juarendra/ERGODASH-MOD-ENCH-OLED-QMK_VIA/Hardware/PCB/Rev1.2/ergodash.kicad_sch

## KiCad design Hardware/PCB/Rev1.2/ergodash.kicad_sch (2024-04-25)

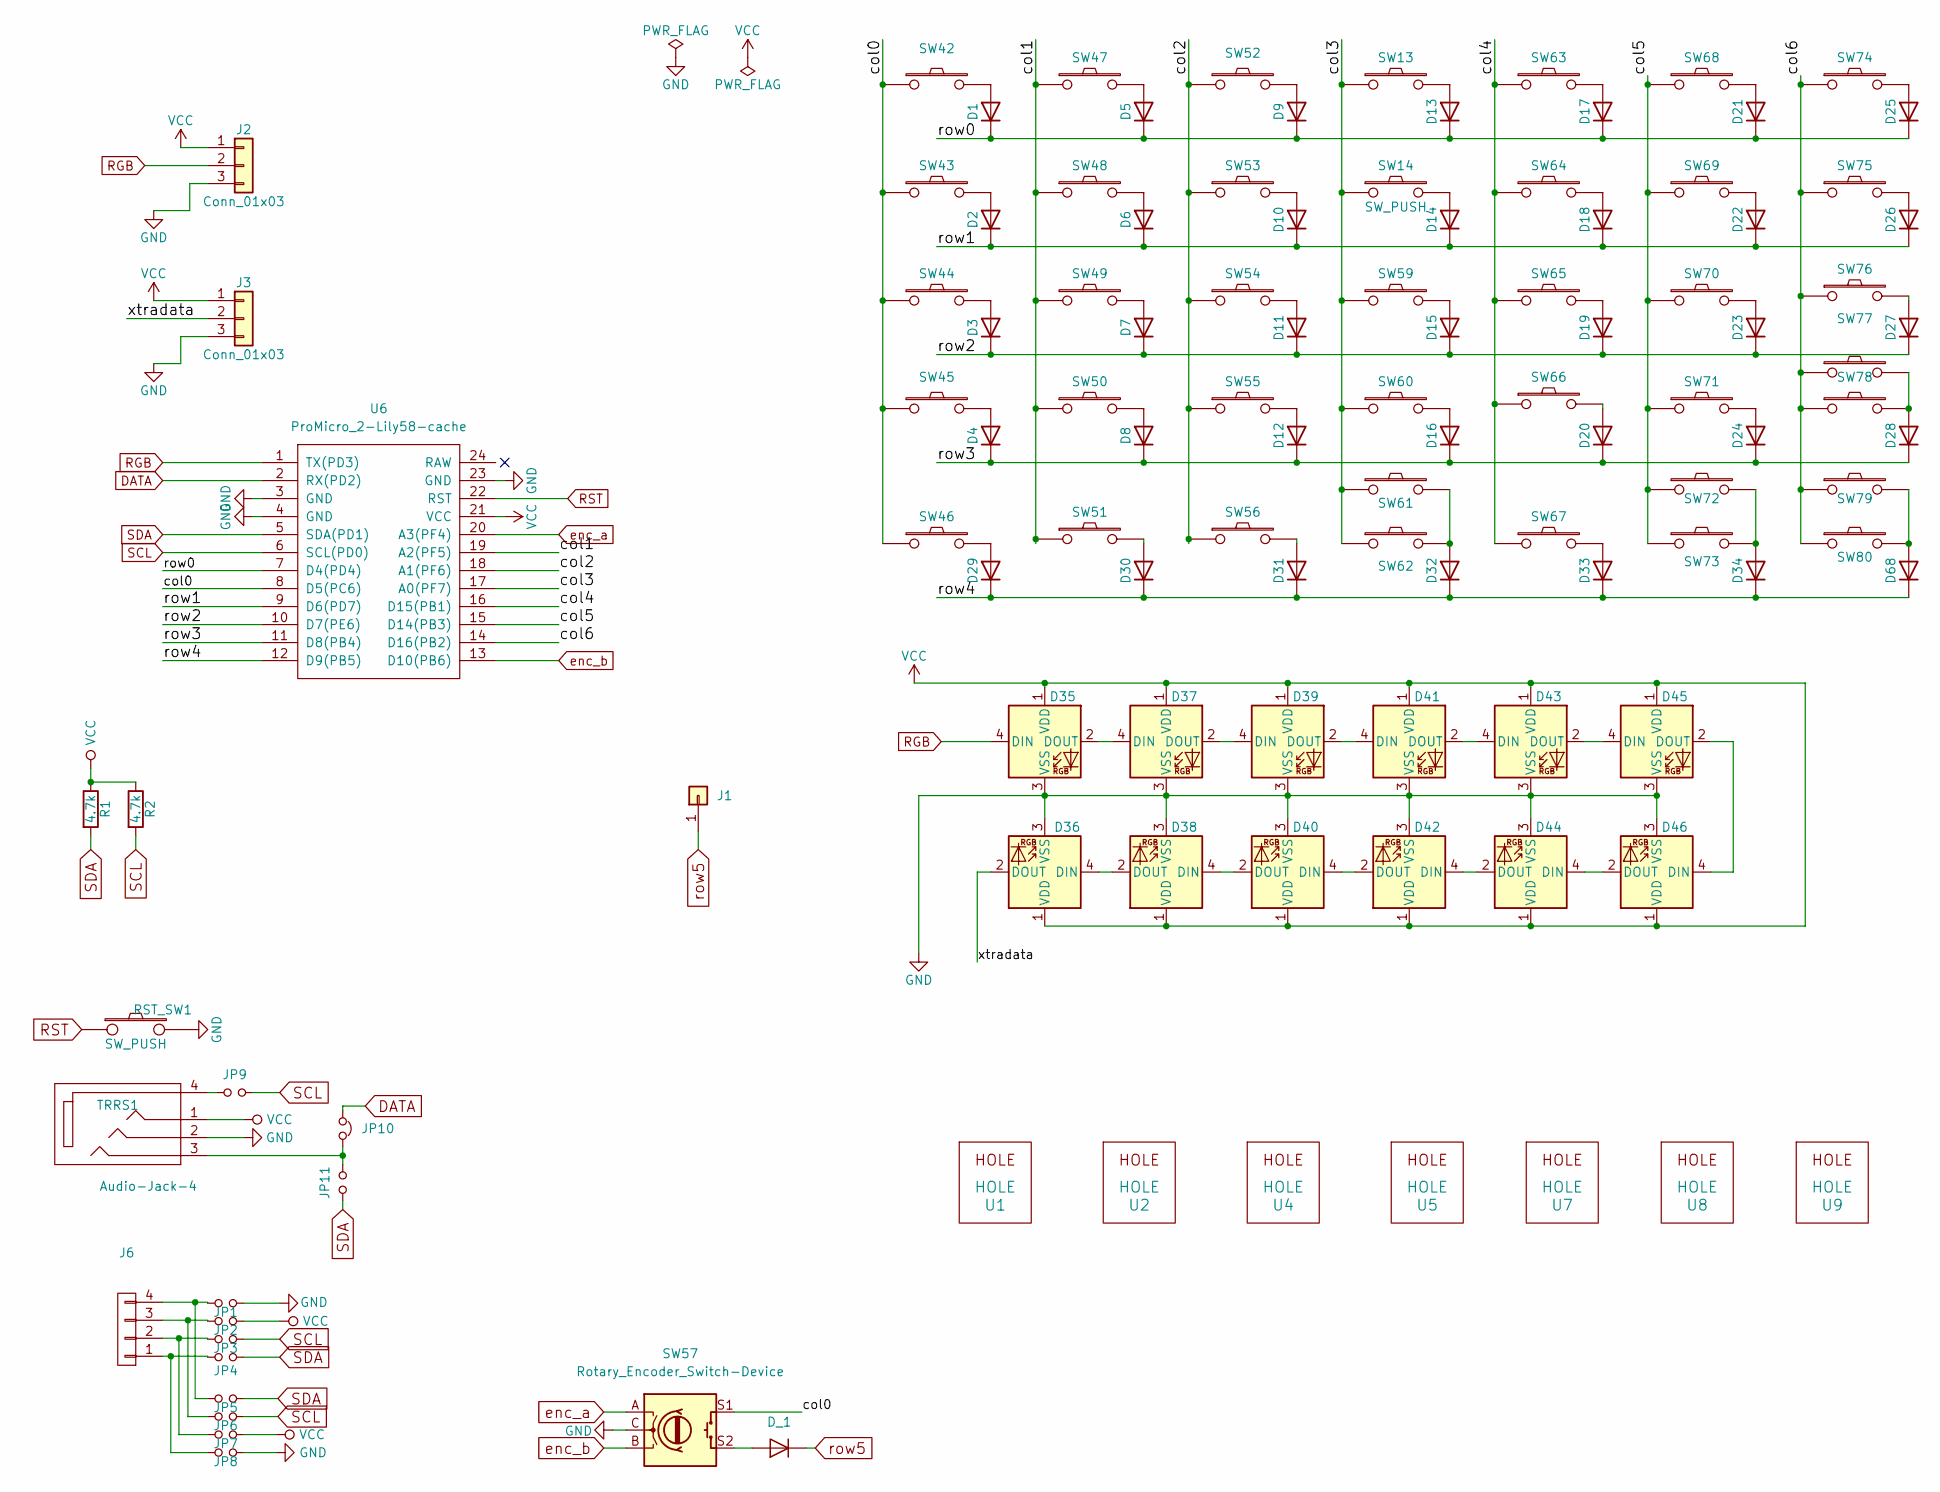
[picture p28: schematic ergodash.kicad_sch]

Parts:
D1, D2, D3, D4, D5, D6, D7, D8, D9, D10, D11, D12, D13, D14, D15, D16, D17, D18, D19, D20, D21, D22, D23, D24, D25, D26, D27, D28, D29, D30, D31, D32, D33, D34, D68: D; Diode_SOD123
D35, D36, D37, D38, D39, D40, D41, D42, D43, D44, D45, D46: YAEMK_SK6812MINI-E; SK6812_mini_e_flipable
D_1: D-Lily58-cache; Diode_SOD123
J1: i2c_pin-Lily58-cache; 1pin_conn
J2, J3: Conn_01x03; conn3
J6: OLED-Lily58-cache; OLED_4Pin
JP1, JP2, JP3, JP4, JP5, JP6, JP7, JP8, JP9, JP11: Jumper_NO_Small-Device; Jumper
JP10: Jumper_NC_Small-Device; jumper_data
R1, R2: 4.7k; R_1206_DoubleSided
RST_SW1: SW_PUSH; TACT_SWITCH_TVBP06
SW13, SW14: SW_PUSH; MX_ALPS
SW42, SW43, SW44, SW45, SW46, SW47, SW48, SW49, SW50, SW51, SW52, SW53, SW54, SW55, SW56, SW59, SW60, SW61, SW62, SW63, SW64, SW65, SW66, SW67, SW68, SW69, SW70, SW71, SW72, SW73, SW74, SW75, SW76, SW77, SW78, SW79, SW80: SW_PUSH-Lily58-cache; CherryMX_Hotswap
SW57: Rotary_Encoder_Switch-Device; RotaryEncoder_Alps_EC11E-Switch_Vertical_H20mm-keebio_modif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
TRRS1: Audio-Jack-4; MJ-4PP-9
U1, U2, U4, U5, U7, U8, U9: HOLE; hole
U6: ProMicro_2-Lily58-cache; ArduinoProMicro-ZigZag-DoubleSided

Connections:
DATA: JP10.1, U6.2 (RX(PD2))
GND: D35.3 (VSS), D36.3 (VSS), D37.3 (VSS), D38.3 (VSS), D39.3 (VSS), D40.3 (VSS), D41.3 (VSS), D42.3 (VSS), D43.3 (VSS), D44.3 (VSS), D45.3 (VSS), D46.3 (VSS), J2.3, J3.3, JP1.1, JP8.1, RST_SW1.2, SW57.C, TRRS1.2, U6.3 (GND), U6.4 (GND), U6.23 (GND)
unnamed: D1.2 (A), SW42.2
unnamed: D2.2 (A), SW43.2
unnamed: D3.2 (A), SW44.2
unnamed: D4.2 (A), SW45.2
unnamed: D5.2 (A), SW47.2
unnamed: D6.2 (A), SW48.2
unnamed: D7.2 (A), SW49.2
unnamed: D8.2 (A), SW50.2
unnamed: D9.2 (A), SW52.2
unnamed: D10.2 (A), SW53.2
unnamed: D11.2 (A), SW54.2
unnamed: D12.2 (A), SW55.2
unnamed: D13.2 (A), SW13.2
unnamed: D14.2 (A), SW14.2
unnamed: D15.2 (A), SW59.2
unnamed: D16.2 (A), SW60.2
unnamed: D17.2 (A), SW63.2
unnamed: D18.2 (A), SW64.2
unnamed: D19.2 (A), SW65.2
unnamed: D20.2 (A), SW66.2
unnamed: D21.2 (A), SW68.2
unnamed: D22.2 (A), SW69.2
unnamed: D23.2 (A), SW70.2
unnamed: D24.2 (A), SW71.2
unnamed: D25.2 (A), SW74.2
unnamed: D26.2 (A), SW75.2
unnamed: D27.2 (A), SW76.2
unnamed: D28.2 (A), SW77.2, SW78.2
unnamed: D29.2 (A), SW46.2
unnamed: D30.2 (A), SW51.2
unnamed: D31.2 (A), SW56.2
unnamed: D32.2 (A), SW61.2, SW62.2
unnamed: D33.2 (A), SW67.2
unnamed: D34.2 (A), SW72.2, SW73.2
unnamed: D35.2 (DOUT), D37.4 (DIN)
unnamed: D36.4 (DIN), D38.2 (DOUT)
unnamed: D37.2 (DOUT), D39.4 (DIN)
unnamed: D38.4 (DIN), D40.2 (DOUT)
unnamed: D39.2 (DOUT), D41.4 (DIN)
unnamed: D40.4 (DIN), D42.2 (DOUT)
unnamed: D41.2 (DOUT), D43.4 (DIN)
unnamed: D42.4 (DIN), D44.2 (DOUT)
unnamed: D43.2 (DOUT), D45.4 (DIN)
unnamed: D44.4 (DIN), D46.2 (DOUT)
unnamed: D45.2 (DOUT), D46.4 (DIN)
unnamed: D68.2 (A), SW79.2, SW80.2
unnamed: D_1.2 (A), SW57.S2
unnamed: J6.1, JP4.2, JP8.2
unnamed: J6.2, JP3.2, JP7.2
unnamed: J6.3, JP2.2, JP6.2
unnamed: J6.4, JP1.2, JP5.2
unnamed: JP9.1, TRRS1.4
unnamed: JP10.2, JP11.2, TRRS1.3
RGB: D35.4 (DIN), J2.2, U6.1 (TX(PD3))
RST: RST_SW1.1, U6.22 (RST)
SCL: JP3.1, JP6.1, JP9.2, R2.2, U6.6 (SCL(PD0))
SDA: JP4.1, JP5.1, JP11.1, R1.2, U6.5 (SDA(PD1))
VCC: D35.1 (VDD), D36.1 (VDD), D37.1 (VDD), D38.1 (VDD), D39.1 (VDD), D40.1 (VDD), D41.1 (VDD), D42.1 (VDD), D43.1 (VDD), D44.1 (VDD), D45.1 (VDD), D46.1 (VDD), J2.1, J3.1, JP2.1, JP7.1, R1.1, R2.1, TRRS1.1, U6.21 (VCC)
col0: SW42.1, SW43.1, SW44.1, SW45.1, SW46.1, SW57.S1, U6.8 (D5(PC6))
col1: SW47.1, SW48.1, SW49.1, SW50.1, SW51.1, U6.19 (A2(PF5))
col2: SW52.1, SW53.1, SW54.1, SW55.1, SW56.1, U6.18 (A1(PF6))
col3: SW13.1, SW14.1, SW59.1, SW60.1, SW61.1, SW62.1, U6.17 (A0(PF7))
col4: SW63.1, SW64.1, SW65.1, SW66.1, SW67.1, U6.16 (D15(PB1))
col5: SW68.1, SW69.1, SW70.1, SW71.1, SW72.1, SW73.1, U6.15 (D14(PB3))
col6: SW74.1, SW75.1, SW76.1, SW77.1, SW78.1, SW79.1, SW80.1, U6.14 (D16(PB2))
enc_a: SW57.A, U6.20 (A3(PF4))
enc_b: SW57.B, U6.13 (D10(PB6))
row0: D1.1 (K), D5.1 (K), D9.1 (K), D13.1 (K), D17.1 (K), D21.1 (K), D25.1 (K), U6.7 (D4(PD4))
row1: D2.1 (K), D6.1 (K), D10.1 (K), D14.1 (K), D18.1 (K), D22.1 (K), D26.1 (K), U6.9 (D6(PD7))
row2: D3.1 (K), D7.1 (K), D11.1 (K), D15.1 (K), D19.1 (K), D23.1 (K), D27.1 (K), U6.10 (D7(PE6))
row3: D4.1 (K), D8.1 (K), D12.1 (K), D16.1 (K), D20.1 (K), D24.1 (K), D28.1 (K), U6.11 (D8(PB4))
row4: D29.1 (K), D30.1 (K), D31.1 (K), D32.1 (K), D33.1 (K), D34.1 (K), D68.1 (K), U6.12 (D9(PB5))
row5: D_1.1 (K), J1.1
xtradata: D36.2 (DOUT), J3.2
